Team-Flex-UoM/digital-oscilloscope/trials/WebSocket8266/WebSocket8266.ino

#include <ESP8266WiFi.h>
#include <WiFiClient.h>
#include <ESP8266WebServer.h>
#include <ESP8266mDNS.h>

#ifndef STASSID
#define STASSID "DT4G"
#define STAPSK "iuytrewq"
#endif

const char* ssid = "DT4G";
const char* password = "iuytrewq";

/*  ============================================================================================================

    Sample code for create a websocket on an ESP8266 board.

    For more info, please watch my video at https://youtu.be/fREqfdCphRA
    MrDIY.ca

  ============================================================================================================== */

#include <Arduino.h>
#include <ESP8266WiFi.h>
#include <ESP8266WiFiMulti.h>
#include <WebSocketsServer.h>
#include <ESP8266WebServer.h>
#include <Hash.h>

String old_value, value;

ESP8266WiFiMulti WiFiMulti;
ESP8266WebServer server(80);
WebSocketsServer webSocket = WebSocketsServer(81);

char html_template[] PROGMEM = R"=====(
<html lang="en">
   <head>
      <meta charset="utf-8">
      <meta name="viewport" content="width=device-width, initial-scale=1">
      <title>MrDIY Socket Example</title>
      <script>
        socket = new WebSocket("ws:/" + "/" + location.host + ":81");
        socket.onopen = function(e) {  console.log("[socket] socket.onopen "); };
        socket.onerror = function(e) {  console.log("[socket] socket.onerror "); };
        socket.onmessage = function(e) {  
            console.log(e.data);
            //document.getElementById("mrdiy_value").innerHTML = e.data;
        };
      </script>
   </head>
   <body style="max-width:400px;margin: auto;font-family:Arial, Helvetica, sans-serif;text-align:center">
      <div><h1><br />My Value</h1></div>
      <div><p id="mrdiy_value" style="font-size:100px;margin:0"></p></div>
   </body>
</html>
)=====";


void webSocketEvent(uint8_t num, WStype_t type, uint8_t* payload, size_t length) {

  switch (type) {
    case WStype_DISCONNECTED:
      Serial.printf("[%u] Disconnected!\n", num);
      break;

    case WStype_CONNECTED:
      {
        IPAddress ip = webSocket.remoteIP(num);
        Serial.printf("[%u] Connected from %d.%d.%d.%d url: %s\n", num, ip[0], ip[1], ip[2], ip[3], payload);
        // send message to client
        webSocket.sendTXT(num, "0");
      }
      break;

    case WStype_TEXT:
      Serial.printf("[%u] get Text: %s\n", num, payload);
      // send message to client
      // webSocket.sendTXT(num, "message here");
      // send data to all connected clients
      // webSocket.broadcastTXT("message here");
      break;

    case WStype_BIN:
      Serial.printf("[%u] get binary length: %u\n", num, length);
      hexdump(payload, length);
      // send message to client
      // webSocket.sendBIN(num, payload, length);
      break;
  }
}

void setup() {

  Serial.begin(115200);
  delay(1000);
  Serial.print("Start");
  WiFiMulti.addAP(STASSID, STAPSK);

  while (WiFiMulti.run() != WL_CONNECTED) {
    Serial.print('.');
    delay(100);
  }



  Serial.println(WiFi.localIP());

  webSocket.begin();
  webSocket.onEvent(webSocketEvent);

  server.on("/", handleMain);
  server.onNotFound(handleNotFound);
  server.begin();
}

void handleMain() {
  server.send_P(200, "text/html", html_template);
}
void handleNotFound() {
  server.send(404, "text/html", "<html><body><p>404 Error</p></body></html>");
}

void loop() {

  webSocket.loop();
  server.handleClient();

  value = (String)micros();
  webSocket.broadcastTXT(value);
  // delay(50);
}
