Team-Flex-UoM/digital-oscilloscope/trials/Serial328/Serial328.ino

/*
 * Copyright (c) 2018, circuits4you.com
 * All rights reserved.
 * Create a TCP Server on ESP8266 NodeMCU.
 * TCP Socket Server Send Receive Demo
 */

//=======================================================================
//                    Power on setup
//=======================================================================
void setup()
{
  Serial.begin(500000);
  Serial.print("Serial");
}
//=======================================================================
//                    Loop
//=======================================================================

void loop()
{
  int a = analogRead(A0);
  Serial.println(millis());
}
//=======================================================================
